Taro-Hayashi/e-ink-display-Stand/xiao-esp32c3-display/secrets.h

#pragma once

#define WIFI_SSID "your-wifi-ssid"
#define WIFI_PASSWORD "your-wifi-password"

// Start ../image-render/apod_api.py on the Mac first.
#define IMAGE_HOST "your-image-host"
#define IMAGE_PORT 8765
#define IMAGE_PATH "/apod_image.bin"
